elipsitz/internet-connected-pinball/controller/src/log.cpp

#include <stdio.h>

#include <Arduino.h>

#include "log.h"

#define MAX_LOG_LINES (32)

std::deque<String> logs;

void log_init()
{
    Serial.begin();
}

void log_log(const char* tag, const char* format, ...)
{
    if (logs.size() == MAX_LOG_LINES) {
        logs.pop_front();
    }
    String formatted;
    
    uint32_t time = millis();
    char buffer[128];
    int len = snprintf(buffer, sizeof(buffer), "[%5d.%03d][%8.8s] ", time / 1000, time % 1000, tag);
    formatted.concat(buffer, len);

    va_list args;
    va_start(args, format);
    len = vsnprintf(buffer, sizeof(buffer), format, args);
    if (len > 0) {
        if (len >= sizeof(buffer)) {
            len = sizeof(buffer) - 1;
        }
        formatted.concat(buffer, len);
    }
    va_end(args);

    Serial.println(formatted);
    logs.push_back(formatted);
}

std::deque<String>& log_get_logs()
{
    return logs;
}
