elipsitz/internet-connected-pinball/controller/src/secrets.example.h

// Device hostname
#define CONFIG_HOSTNAME "pinball-scores"

// Webserver host
#define CONFIG_WEB_HOST ""
// Webserver port
#define CONFIG_WEB_PORT 80
// Webserver TLS
#define CONFIG_WEB_HTTPS false
// Webserver API endpoint
#define CONFIG_WEB_ADD_SCORE_ENDPOINT "/api/v1/add_score"
// Webserver API auth token
#define CONFIG_WEB_AUTH "Bearer <token>"

// Wifi network SSID
#define CONFIG_WIFI_SSID ""
// Wifi network password
#define CONFIG_WIFI_PASS ""
